FaqT0tum/Orbion_Space_Mouse_OLD/Your_creations/Orbion_Arcade_By-AFUDirk/IMG/Orbion_arcade_knob.jpg

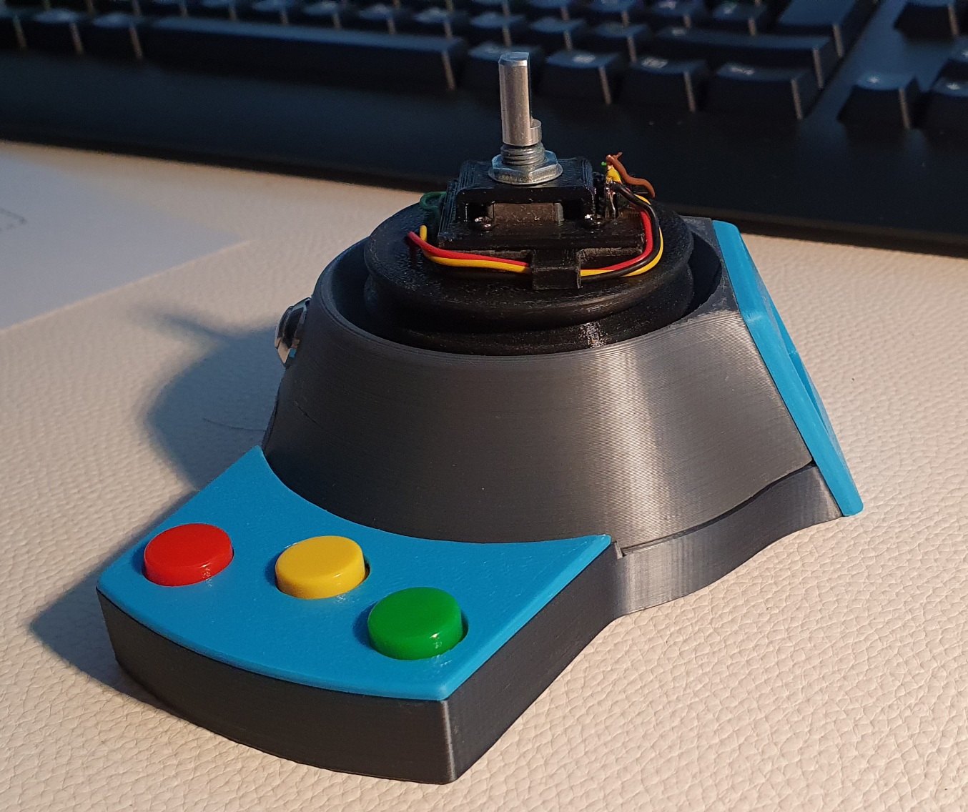
Your_creations/Orbion_Arcade_By-AFUDirk/IMG/Orbion_arcade_knob.jpg
