FaqT0tum/Orbion_Space_Mouse_OLD/Your_creations/Orbion_Arcade_By-AFUDirk/Orbion_STL/Slicer/Ex_Width.png

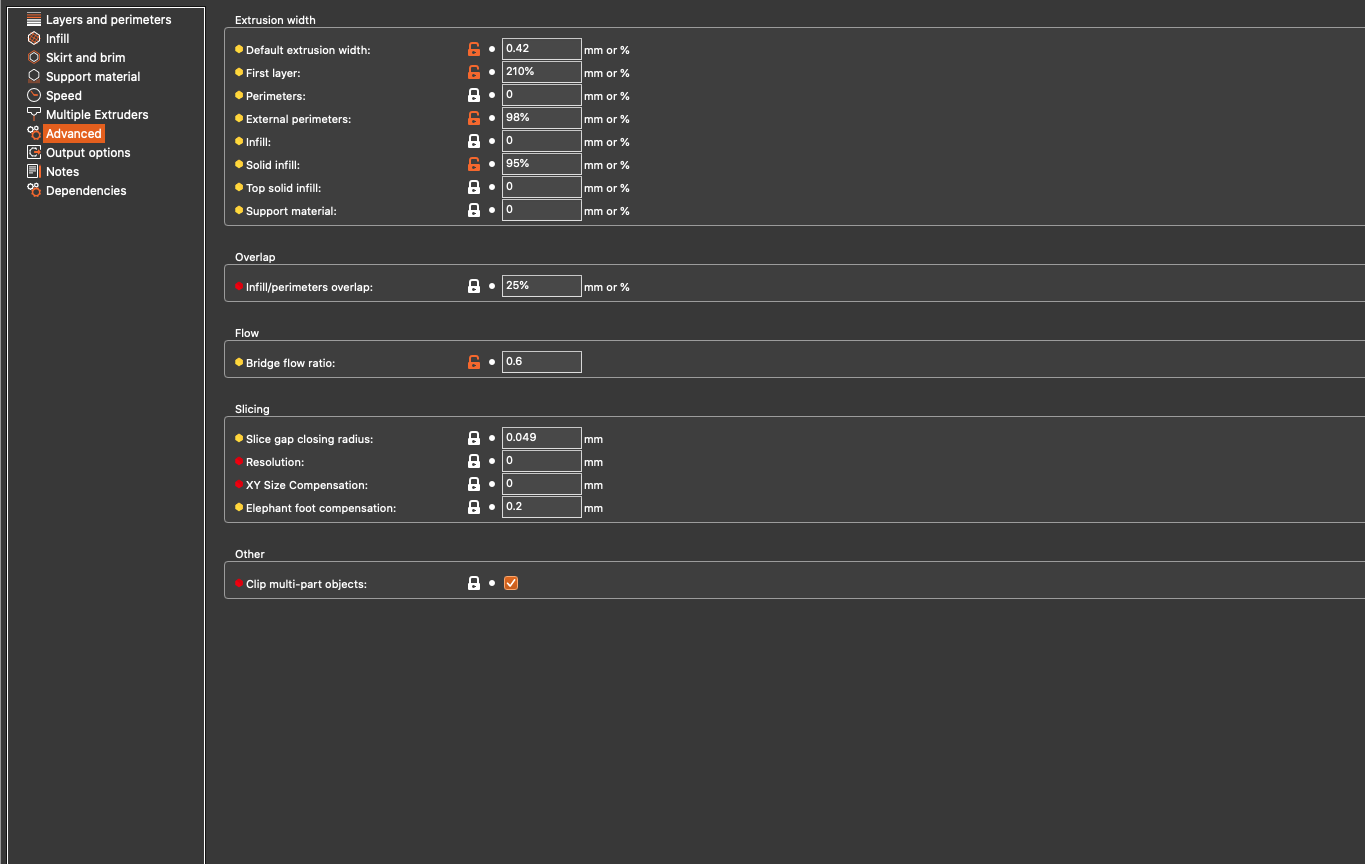
Your_creations/Orbion_Arcade_By-AFUDirk/Orbion_STL/Slicer/Ex_Width.png
