FaqT0tum/Orbion_Space_Mouse_OLD/Your_creations/Orbion_Arcade_By-AFUDirk/Orbion_STL/Orbion_Rev2.2_Macroboard/Shell_Macroboard li.stl

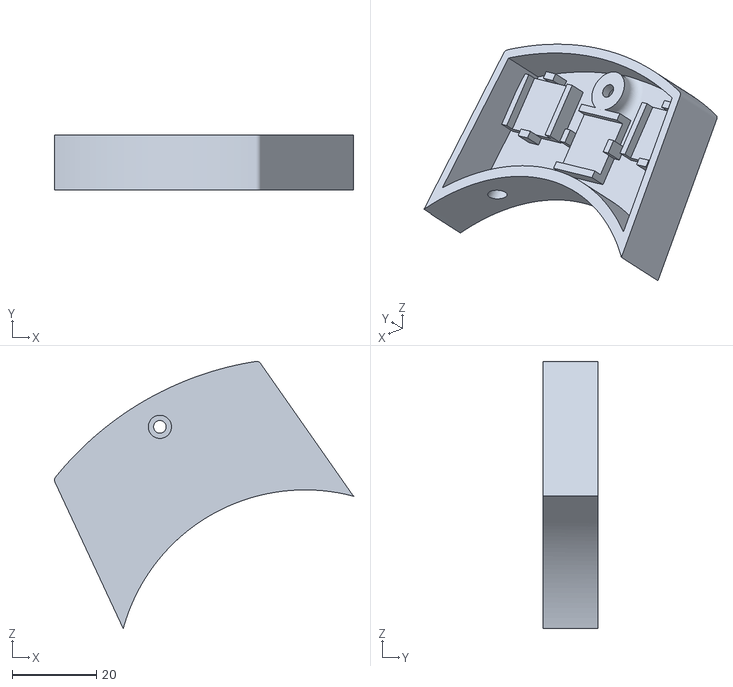
[picture p41: CAD file, 2022-02-23]
Your_creations/Orbion_Arcade_By-AFUDirk/Orbion_STL/Orbion_Rev2.2_Macroboard/Shell_Macroboard li.stl
70.9 x 12.9 x 63.4
