FaqT0tum/Orbion_Space_Mouse_OLD/Orbion_STL/Orbion_Rev2.2/Enc_holder_17.stl

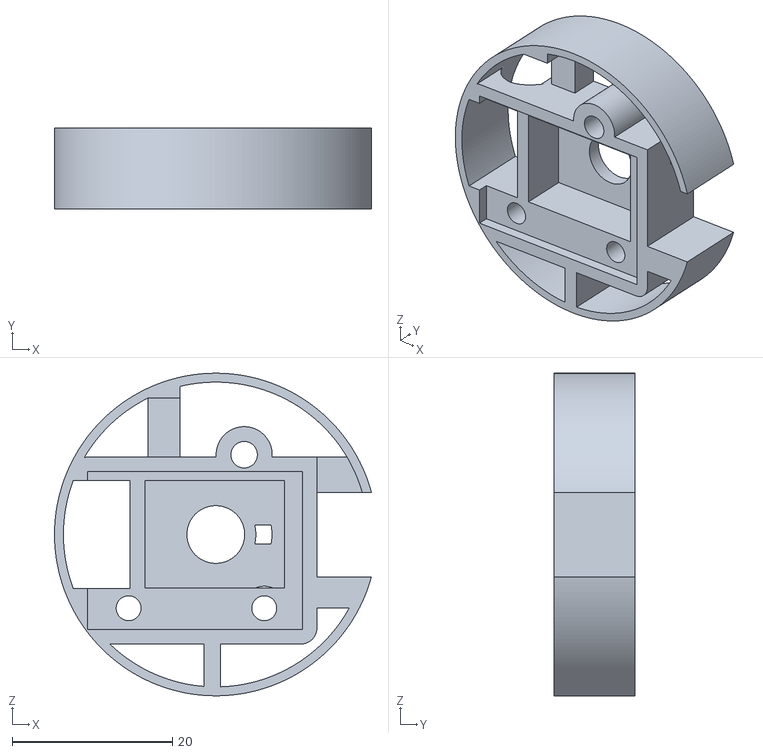
[picture p42: CAD file, 2022-02-09]
Orbion_STL/Orbion_Rev2.2/Enc_holder_17.stl
39.5 x 10.1 x 40.2
