FaqT0tum/Orbion_Space_Mouse_OLD/Orbion_STL/Orbion_Rev2.2/Sceen_cover.stl

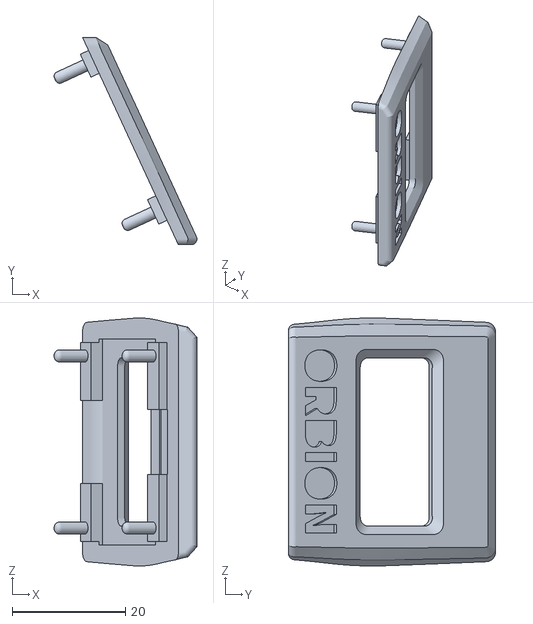
[picture p43: CAD file, 2022-02-09]
Orbion_STL/Orbion_Rev2.2/Sceen_cover.stl
25.2 x 36.6 x 43.7
