FaqT0tum/Orbion_Space_Mouse_OLD/Your_creations/Orbion_Arcade_By-AFUDirk/Orbion_STL/Enc_Klemme.stl

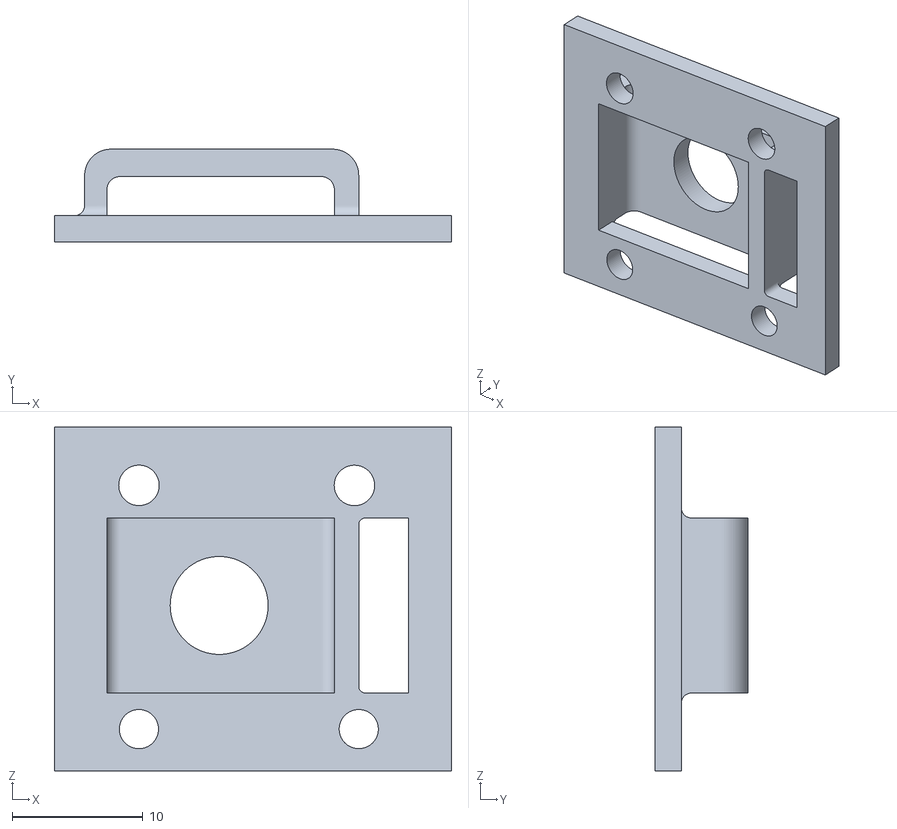
[picture p44: CAD file, 2022-02-23]
Your_creations/Orbion_Arcade_By-AFUDirk/Orbion_STL/Enc_Klemme.stl
30.4 x 7.10 x 26.3
