FaqT0tum/Orbion_Space_Mouse_OLD/Your_creations/Orbion_Arcade_By-AFUDirk/Orbion_STL/Knob_Base.stl

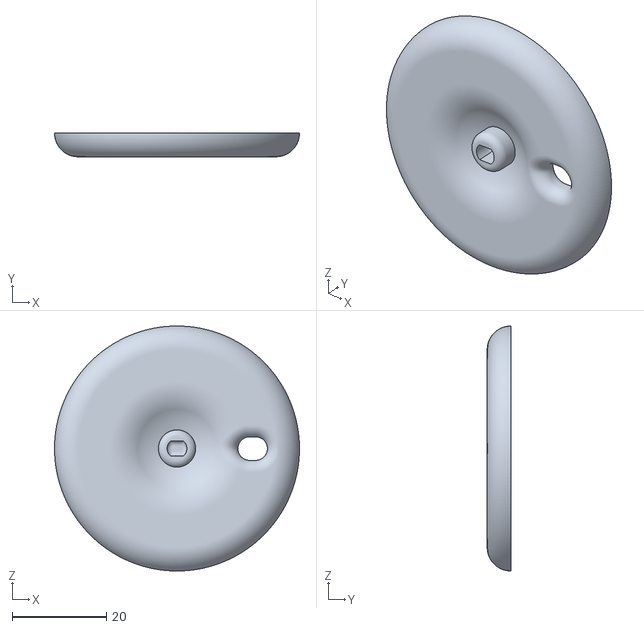
[picture p45: CAD file, 2021-06-29]
Your_creations/Orbion_Arcade_By-AFUDirk/Orbion_STL/Knob_Base.stl
52.0 x 5.01 x 52.0
