FaqT0tum/Orbion_Space_Mouse_OLD/Your_creations/Orbion_Arcade_By-AFUDirk/Orbion_STL/Base.stl

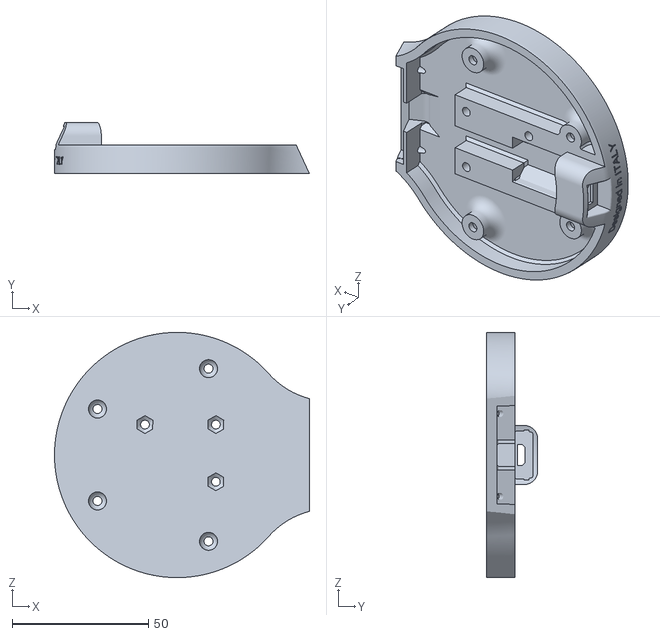
[picture p46: CAD file, 2021-06-24]
Your_creations/Orbion_Arcade_By-AFUDirk/Orbion_STL/Base.stl
93.6 x 18.9 x 90.0
