FaqT0tum/Orbion_Space_Mouse_OLD/Your_creations/Orbion_Arcade_By-AFUDirk/Orbion_STL/Body.stl

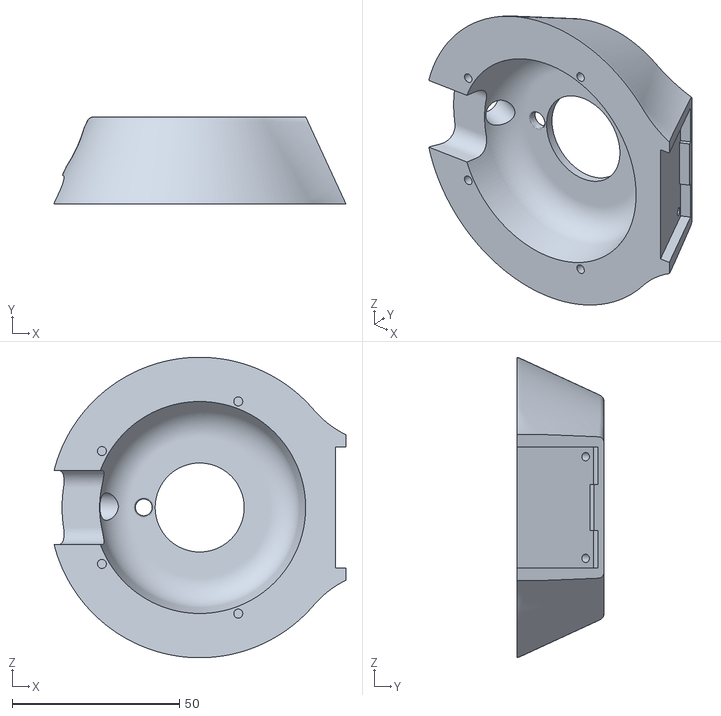
[picture p48: CAD file, 2021-06-24]
Your_creations/Orbion_Arcade_By-AFUDirk/Orbion_STL/Body.stl
87.2 x 26.0 x 89.7
