FaqT0tum/Orbion_Space_Mouse_OLD/Your_creations/Orbion_Arcade_By-AFUDirk/Orbion_STL/Orbion_Rev2.1/Enc_holder_17.stl

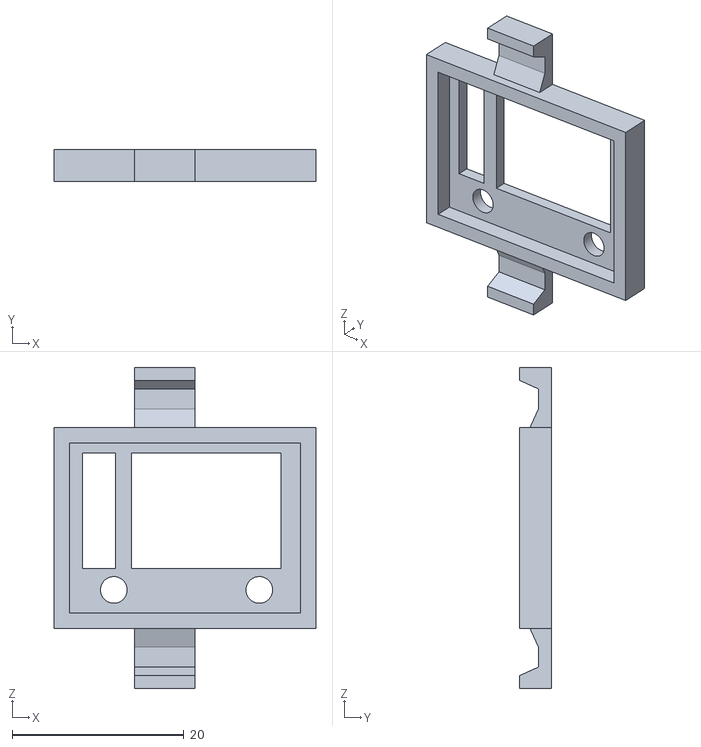
[picture p49: CAD file, 2022-01-21]
Your_creations/Orbion_Arcade_By-AFUDirk/Orbion_STL/Orbion_Rev2.1/Enc_holder_17.stl
30.4 x 3.70 x 37.3
