FaqT0tum/Orbion_Space_Mouse_OLD/Your_creations/Orbion_Arcade_By-AFUDirk/Orbion_STL/Support_micro_joystick.stl

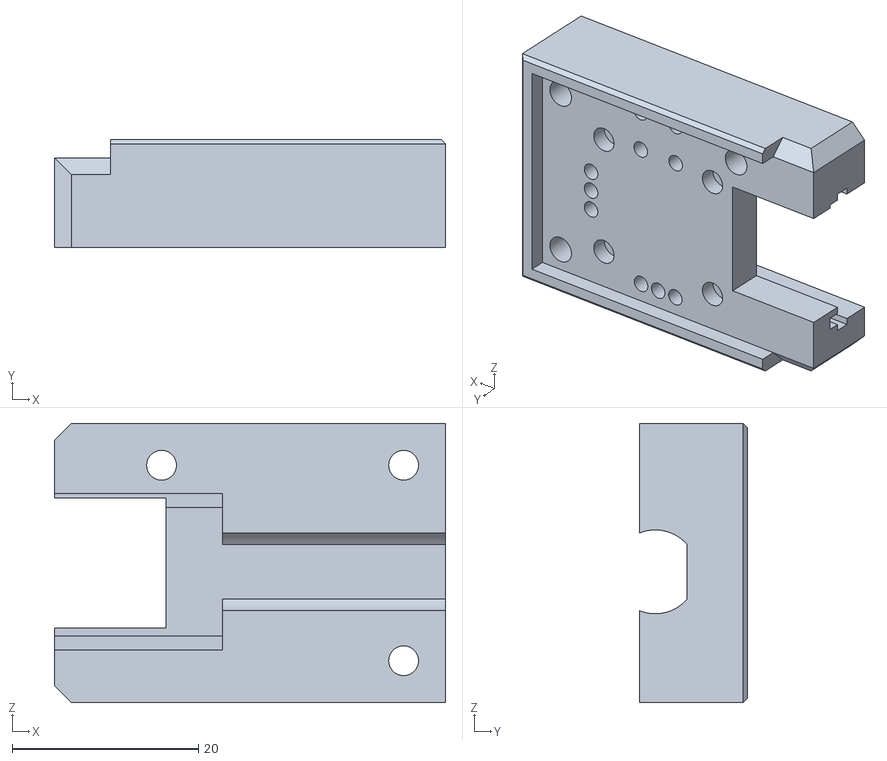
[picture p50: CAD file, 2021-06-24]
Your_creations/Orbion_Arcade_By-AFUDirk/Orbion_STL/Support_micro_joystick.stl
42.0 x 11.6 x 30.0
