FaqT0tum/Orbion_Space_Mouse_OLD/Your_creations/Orbion_Arcade_By-AFUDirk/Orbion_STL/Orbion_Rev2.1/Supp_ele.stl

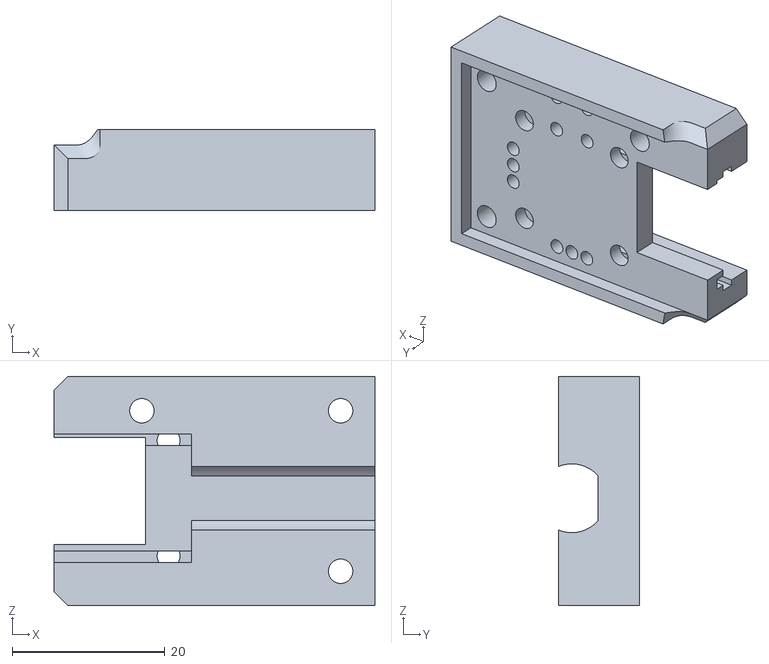
[picture p51: CAD file, 2022-01-21]
Your_creations/Orbion_Arcade_By-AFUDirk/Orbion_STL/Orbion_Rev2.1/Supp_ele.stl
42.0 x 10.5 x 30.0
